wdathing/one-rom/hardware/3d/README.md

# One ROM 3D Models

This directory contains 3D printable models that may be useful for One ROM users.

All files in this directory tree are licensed under the [CERN Open Hardware Licence Version 2 - Weakly Reciprocal (CERN-OHL-W-2.0)](/LICENSE.md#cern-ohl-w-20-license).  See the [LICENSE](/LICENSE.md#cern-ohl-w-20-license) and [NOTICE](/hardware/NOTICE) files in the root of the repository for more details.
