wdathing/one-rom/hardware/pcb/verified/fire-24-g/README.md

# Fire 24 Rev G

An upright USB-C variant of fire-24-f - the connector sticks up out of the board rather than lying flat, which helps where there is too little room at the edge of One ROM to plug in a cable.  It is not preferred over fire-24-f - the two connector orientations are complementary.
