wdathing/one-rom/hardware/pcb/verified/fire-28-d/README.md

# Fire 28 Rev D

An upright USB-C variant of fire-28-c - the connector sticks up out of the board rather than lying flat, which helps where there is too little room at the edge of One ROM to plug in a cable.  It is not preferred over fire-28-c - the two connector orientations are complementary.

**Has components on both sides of the board.**
