wdathing/one-rom/hardware/pcb/verified/fire-32-c/README.md

# Fire 32 Rev C

An upright USB-C variant of fire-32-b2 - the connector sticks up out of the board rather than lying flat, which helps where there is too little room at the edge of One ROM to plug in a cable.  It is not preferred over fire-32-b2 - the two connector orientations are complementary.

**Has components on both sides of the board.**
