wdathing/one-rom/firmware/src/main.c

// One ROM Main startup code (clock and GPIO initialisation)

// Copyright (C) 2026 Piers Finlayson <piers@piers.rocks>
//
// MIT License

#include "include.h"
#ifdef UART_BOOT_TEST
#include "reg-rp235x.h"
#endif

int firmware_main(void) {
    // Platform specific initialization
    platform_specific_init();

    // Next step is to validate the minimum metadata required to continue.
    // Beyond here, code can assume onerom_info.metadata_header is present
    // and valid, as are ->hardware_info and ->firmware_config.
    if (!metadata_valid()) {
        // Enter bootloader
        ERR("Invalid metadata");
        enter_bootloader();
    }

    // Update any runtime info based on the metadata.
    update_runtime_from_metadata();

    // Next initialize the GPIOs very early on, to turn off the status LED and
    // read the ROM slot select pins.  Pins are part of the metadata, which is
    // why we had to check that first.
    setup_initial_gpios();

    // Enable logging.  Done after GPIO setup, so SWD pins are configured.
    if (BOOT_LOGGING_EN && !TURBO) {
        LOG_INIT();
    }

    // Do initial plugin parsing.  The system plugin can potentially override
    // USB DFU support, which is why we do it now.
    // Must be done even when turbo booting.
    DEBUG("Initial plugin parse");
    uint8_t disable_vbus_det, plugins, num_plugins;
    plugins = initial_plugin_parse(&disable_vbus_det, &num_plugins);

    // Set up VBUS detect interrupt if there's no plugin replacing USB
    // support.
    if (!disable_vbus_det) {
        DEBUG("Init VBUS det");
        setup_vbus_interrupt();
    } else {
        LOG("Plugin disabled VBUS detect");
    }

    // Log ROM slot information
    if (BOOT_LOGGING_EN && !TURBO) {
        log_roms();
    }

    // If turbo booting, skip the image select jumper reading
    uint32_t sel_mask = 0;
    uint32_t sel_pins = 0;
    if (!TURBO) {
        // Read image select pin values, as this allows us to figure out what
        // ROM slot to serve, which in turn might have some firmware configuration
        // overrides, like overclocking.
        sel_pins = check_sel_pins(&sel_mask);
    }

    // Get the chosen ROM slot based on the image select pins.
    if (METADATA->rom_slot_count > num_plugins) {
        // Figure out what ROM slot to use
        RUNTIME->rom_slot_index = get_rom_slot_index(sel_pins, sel_mask, plugins);

        // Get pointer to the selected ROM slot
        RUNTIME->current_rom_slot = &ROM_SLOTS[RUNTIME->rom_slot_index];

        // Now process any firmware overrides from the selected ROM slot.
        process_firmware_overrides(RUNTIME->current_rom_slot);
    } else {
        ERR("No ROM slots to serve");
    }

    // Initialize clock
    DEBUG("Init clock");
    setup_clock();

#ifdef UART_BOOT_TEST
    // Bring-up test only: continuously transmit 0x55 on UART1 (GPIO40 TX /
    // GPIO41 RX) from here - after clock setup, so RUNTIME->sysclk_mhz is
    // valid, but before ROM serving (PIOs/DMA) or any plugin ever starts.
    // Isolates UART1 bring-up completely from both.  Never returns.
    {
        CLOCK_PERI_CTRL = CLOCK_PERI_CTRL_ENABLE;

        RESET_RESET_SET = RESET_UART1;
        RESET_RESET_CLR = RESET_UART1;
        while (!(RESET_DONE & RESET_UART1)) { }

        GPIO_CTRL(40u) = GPIO_CTRL_FUNC_UART;
        GPIO_CTRL(41u) = GPIO_CTRL_FUNC_UART;
        // PAD_INPUT set on TX too, not just RX - confirmed against the SDK's
        // own gpio_set_function(), which enables the pad input buffer
        // unconditionally on every pin, output-only or not.
        GPIO_PAD(40u) = (GPIO_PAD(40u) | PAD_INPUT) & ~(uint32_t)(PAD_PU | PAD_PD | PAD_OUTPUT_DISABLE | PAD_ISO);
        GPIO_PAD(41u) = (GPIO_PAD(41u) | PAD_INPUT) & ~(uint32_t)(PAD_PU | PAD_PD | PAD_OUTPUT_DISABLE | PAD_ISO);

        uint32_t clk_peri_hz = (uint32_t)RUNTIME->sysclk_mhz * 1000000u;
        uint32_t baud = 115200u;
        uint64_t scaled = ((uint64_t)clk_peri_hz * 4u + (baud / 2u)) / baud;
        uint32_t ibrd = (uint32_t)(scaled >> 6);
        uint32_t fbrd = (uint32_t)(scaled & 0x3Fu);
        if (ibrd == 0u) {
            ibrd = 1u;
            fbrd = 0u;
        }

        UART_REG(UART1_BASE, UART_CR_OFFSET) = 0;
        UART_REG(UART1_BASE, UART_IBRD_OFFSET) = ibrd;
        UART_REG(UART1_BASE, UART_FBRD_OFFSET) = fbrd;
        UART_REG(UART1_BASE, UART_LCR_H_OFFSET) = UART_LCR_H_WLEN_8 | UART_LCR_H_FEN;
        UART_REG(UART1_BASE, UART_CR_OFFSET) = UART_CR_UARTEN | UART_CR_TXE | UART_CR_RXE;

        for (;;) {
            while (UART_REG(UART1_BASE, UART_FR_OFFSET) & UART_FR_TXFF) { }
            UART_REG(UART1_BASE, UART_DR_OFFSET) = 0x55u;
        }
    }
#endif // UART_BOOT_TEST

    // Set up the RAM table to serve the ROM from
    if (RUNTIME->current_rom_slot != NULL) {
        // We always preload to RAM slot 0
        RUNTIME->current_ram_slot = 0;

        preload_rom_image();
    }

    // Set up the status LED hardware now (unconditionally - the pin is
    // configured as an output whether or not the LED is currently on), so we
    // don't need to call the function from the main loop, which might be
    // running from RAM.
    DEBUG("Init LED");
    setup_status_led();

    // If no ROM slot is selected, enter limp mode now that the status LED is
    // setup.
    if (RUNTIME->current_rom_slot == NULL) {
        limp_mode(LIMP_MODE_NO_ROMS);
    }

    // Put the status LED where the configuration says, now we're ready to
    // serve the ROM.
    pio_led_boot();

    // Start serving the ROM.  This returns once the PIOs and DMAs have been
    // setup.  We return back to the reset handler in vector.c, which then
    // starts any plugins.  We do it from higher up the stack, so the minimum
    // stack is used for any plugin running on this core. 
    LOG("Setup ROM serving");

    // Shut SWD down before serving starts, if configured to do so.  Done last
    // so a probe is available for all of boot - including boot logging, which
    // rides RTT over SWD.  Nothing is logged beyond this point, and plugins
    // (started from vector.c once pio() returns) get no logging either.
    //
    // Cheap enough - a RAM test and a few register writes - to do even when
    // turbo booting.
    if (!RUNTIME->swd_enabled) {
        LOG("Disabling SWD");
        disable_swd();
    }

    return pio();
}
