wdathing/one-rom/docs/pdf/render.py

#!/usr/bin/env python3
"""Render the One ROM documentation set to PDF.

The set, and every string that appears in a PDF but not in its source markdown,
is defined in docs.toml.  Nothing document-specific is written here.

Cover text comes from the document itself: the title is the markdown's leading
H1 and the subtitle is the paragraph that follows it.  Every One ROM document
already opens by naming itself and saying in a sentence what it covers, so a
second copy of that text kept alongside the build would only be a copy to let
drift.  The H1 is dropped from the body, since the cover now carries it.

A document assembled from several markdown files is the exception: no one member
names the whole, so its cover text is declared in docs.toml, and every member
keeps its own H1 as a top-level heading.  This renders one file either way -
the assembling is done before this runs, by
`cargo run -p doc-gen --bin doc-assemble`, which writes <slug>.md into the same
output directory.  ci/build-docs.sh runs the two in order.  Neither calls the
other.

A manifest of what was built is written to the output directory, for
ci/build-docs.sh to stage from.
"""

import argparse
import datetime
import json
import re
import subprocess
import sys
import tomllib
from pathlib import Path

PDF_DIR = Path(__file__).resolve().parent

# A title may name the version of the thing it documents - COMPATIBILITY.md
# opens "One ROM Chip Compatibility - firmware v0.7.2".  The cover prints the
# version in its own right, so trim the clause rather than saying it twice.
TITLE_VERSION_CLAUSE = re.compile(r"\s*[-–—]\s*\S*\s*v\d+\.\d+\.\d+\s*$")

# Contents entries long enough to wrap read badly, and in CHIP-TYPES.md every
# pinout heading is "23QL384 - A composite ROM type, serving a combined ...".
# The body keeps the full heading, where the description earns its place - the
# contents keeps the part that identifies it.
TOC_TRUNCATE_OVER = 40
TOC_SPLIT = re.compile(r"\s+[-–—]\s+")

# A document written for GitHub may carry its own hand-written contents list,
# as CHIP-TYPES.md does.  The generated contents supersedes it, so it is
# dropped rather than printed twice.
HAND_WRITTEN_TOC = re.compile(r"^#{1,3}\s+(table of )?contents\s*$", re.I)

# How deep the contents goes for a document that does not say.  An assembled
# document spends its first level on member titles, so it usually says.
DEFAULT_TOC_DEPTH = 3

# A document may state a value that something else owns - a hold limit from the
# metadata schema, the CLI's own version - inside a marker naming that source:
#
#     the limit is <!--[const:GPIO_MAX_HOLD_MS:seconds]-->60 seconds<!--[/]-->.
#
# rust/doc-gen checks those values against their sources; this only has to take
# the markers back out before rendering, so a PDF carries the text and not the
# bookkeeping.  The delimiters are stated in both places, which is two copies of
# a punctuation choice rather than of a fact - change one and the other's tests
# say so.
MARKER = re.compile(r"<!--\[[^\]]*\]-->|<!--\[/\]-->")
MARKER_OPEN = re.compile(r"<!--\[(?!/)([^\]]*)\]-->")
MARKER_CLOSE = "<!--[/]-->"

NOT_PROSE = re.compile(
    r"""^(
        \#             |   # heading
        >              |   # block quote
        \|             |   # table row
        (```|~~~)      |   # fenced code
        ([-*+]\s)      |   # bullet list - the space matters, since a paragraph
                           # may open with an inline code span or emphasis
        (\d+\.\s)      |   # numbered list
        ([-*_]{3,}$)       # horizontal rule
    )""",
    re.X,
)


def git(root, *args):
    """Run git in the repository and return its trimmed stdout."""
    return subprocess.run(
        ["git", *args], capture_output=True, text=True, check=True, cwd=root,
    ).stdout.strip()


# -------------------------------------------------------------- versions --

def cli_version(root):
    """The onerom-cli crate version."""
    text = (root / "rust/cli/Cargo.toml").read_text()
    match = re.search(r'^version\s*=\s*"([^"]+)"', text, re.M)
    if not match:
        sys.exit("error: no version in rust/cli/Cargo.toml")
    return match.group(1)


def firmware_version(root):
    """The firmware version, from the root Makefile."""
    text = (root / "Makefile").read_text()
    parts = []
    for field in ("MAJOR", "MINOR", "PATCH"):
        match = re.search(rf"^VERSION_{field}\s*:?=\s*(\S+)", text, re.M)
        if not match:
            sys.exit(f"error: no VERSION_{field} in Makefile")
        parts.append(match.group(1))
    return ".".join(parts)


VERSION_READERS = {"cli": cli_version, "firmware": firmware_version}


# -------------------------------------------------------------- markdown --

def check_markers(text, origin):
    """Refuse a document whose markers would print into the PDF."""
    opens = len(MARKER_OPEN.findall(text))
    closes = text.count(MARKER_CLOSE)
    if opens != closes:
        sys.exit(
            f"error: {origin} has {opens} opening and {closes} closing value "
            f"markers.\n  An unclosed marker would print into the PDF.  Run "
            f"'cargo run -p doc-gen' to see where."
        )


def strip_markers(text):
    """The document as a reader sees it, with the value markers removed."""
    return MARKER.sub("", text)


def check_values(root, source, origin):
    """Check the values a document states against the sources that own them.

    Only for a document read from the working tree.  A past edition is read
    from a git ref, where its values are what they were then and the checker
    may not exist at all.

    ci/rust-tests.sh runs the same check, but a release is built by hand and
    the gate may not have been - and this is the last moment before a stale
    number is published as a PDF.
    """
    try:
        result = subprocess.run(
            ["cargo", "run", "-q", "-p", "doc-gen", "--bin", "doc-gen",
             "--", "--check", source],
            cwd=root / "rust",
            capture_output=True,
            text=True,
        )
    except FileNotFoundError:
        sys.exit(
            "error: cargo not found, so the values in "
            f"{origin} cannot be checked against their sources.\n  A document "
            "read from the working tree is checked before it is published.  "
            "Past\n  editions, which name a git ref, are not - build those "
            "without a Rust toolchain."
        )
    if result.returncode != 0:
        sys.exit(
            f"error: {origin} states values that no longer match their "
            f"sources:\n{result.stdout}{result.stderr}"
        )


def is_prose(line):
    """True if a stripped line opens an ordinary paragraph."""
    return not NOT_PROSE.match(line)


def strip_inline_markup(text):
    """Reduce inline markdown to the plain text behind it."""
    text = re.sub(r"\[([^\]]*)\]\([^)]*\)", r"\1", text)  # links
    text = re.sub(r"[`*_]", "", text)
    return text.strip()


def drop_hand_written_toc(lines):
    """Remove a hand-written contents section, up to the next heading."""
    out = []
    skipping = False
    for line in lines:
        if HAND_WRITTEN_TOC.match(line):
            skipping = True
            continue
        if skipping:
            if line.startswith("#"):
                skipping = False
            else:
                continue
        out.append(line)
    return out


def read_document(text, origin):
    """Return (title, subtitle, body) for a markdown document."""
    lines = text.split("\n")

    title = None
    start = 0
    for i, line in enumerate(lines):
        if line.startswith("# "):
            title = TITLE_VERSION_CLAUSE.sub("", strip_inline_markup(line[2:]))
            start = i + 1
            break
    if title is None:
        sys.exit(f"error: {origin} has no leading H1 to use as a title")

    subtitle = ""
    paragraph = []
    for line in lines[start:]:
        stripped = line.strip()
        if not stripped:
            if paragraph:
                break
            continue
        if not is_prose(stripped):
            if paragraph:
                break
            continue
        paragraph.append(stripped)
    if paragraph:
        subtitle = strip_inline_markup(" ".join(paragraph))

    body = drop_hand_written_toc(lines[:start - 1] + lines[start:])
    return title, subtitle, "\n".join(body)


def shorten_toc(html):
    """Trim over-long contents entries to their identifying part."""

    def trim(match):
        opening, text = match.group(1), match.group(2)
        if len(text) > TOC_TRUNCATE_OVER:
            head = TOC_SPLIT.split(text, maxsplit=1)[0]
            if head != text and len(head) >= 3:
                text = head
        return f"{opening}{text}</a>"

    start = html.find('<nav id="TOC"')
    end = html.find("</nav>", start)
    if start < 0 or end < 0:
        return html
    toc = re.sub(r"(<a\b[^>]*>)([^<]*)</a>", trim, html[start:end])
    return html[:start] + toc + html[end:]


# ----------------------------------------------------------------- build --

def members_of(document, slug):
    """The document's members, or None where it names a single source."""
    members = document.get("members")
    if members and "source" in document:
        sys.exit(
            f"error: {slug}: has both source and members.\n  A document is one "
            f"file or a list of them, not both - drop whichever is not what you "
            f"meant."
        )
    if not members and "source" not in document:
        sys.exit(f"error: {slug}: has neither source nor members")
    return members


def render(document, config, root, out_dir, commit, date, year):
    project = config["project"]
    slug = document["slug"]

    version_source = document["version_source"]
    if version_source not in config["version_sources"]:
        sys.exit(f"error: {slug}: unknown version source '{version_source}'")
    spec = config["version_sources"][version_source]

    # A source may state its version outright rather than being read from the
    # tree.  That is what lets a past edition be rebuilt: the working tree says
    # what the CLI is now, not what it was at the ref being rendered.
    if "version" in spec:
        version = spec["version"]
    else:
        version = VERSION_READERS[version_source](root)
    label = spec["label"].format(version=version)

    members = members_of(document, slug)
    ref = document.get("ref")

    # A document may name a git ref, and is then read from the object store
    # rather than the working tree - no checkout, and this tree is untouched.
    # The cover is stamped with that ref's commit, so it does not misattribute
    # the text to whatever HEAD happens to be.
    if members:
        if ref:
            sys.exit(
                f"error: {slug}: names both members and a ref.\n  An assembled "
                f"document is built from the working tree.  A past edition names "
                f"one\n  file, as it shipped."
            )
        sources = [member["source"] for member in members]
        assembled = out_dir / f"{slug}.md"
        if not assembled.exists():
            sys.exit(
                f"error: {slug} is assembled from {', '.join(sources)}, and "
                f"{assembled} is not there.\n  Run 'cargo run -p doc-gen --bin "
                f"doc-assemble -- --out-dir {out_dir}' first, or run\n  "
                f"ci/build-docs.sh, which runs the two in order."
            )
        text = assembled.read_text()
        origin = ", ".join(sources)
        for source in sources:
            check_values(root, source, source)
    elif ref:
        text = git(root, "show", f"{ref}:{document['source']}")
        commit = git(root, "rev-parse", "--short", f"{ref}^{{commit}}")
        origin = f"{ref}:{document['source']}"
    else:
        text = (root / document["source"]).read_text()
        origin = document["source"]
        check_values(root, origin, origin)

    check_markers(text, origin)
    text = strip_markers(text)

    # A document may also state its version in its own prose, for readers of the
    # markdown on GitHub, who get no cover and no versioned filename.  That is a
    # second statement of the same fact, so it is checked rather than trusted -
    # a manual must not be published whose banner disagrees with its cover.
    banner = document.get("version_banner")
    if banner:
        expected = banner.format(version=version)
        if expected not in text:
            sys.exit(
                f"error: {origin} does not say \"{expected}\".\n"
                f"  The version being published is {version}. Update the "
                f"document's own version statement to match, or correct the "
                f"version source."
            )

    if members:
        # Declared rather than read: the cover names the whole document, and no
        # member of it does.  Each member's H1 stays in the body as a top-level
        # heading, so nothing is dropped here.
        for key in ("title", "subtitle"):
            if key not in document:
                sys.exit(
                    f"error: {slug}: is assembled from members, so it needs a "
                    f"{key} - no member names the whole document."
                )
        title = strip_inline_markup(document["title"])
        subtitle = strip_inline_markup(document["subtitle"])
        body = text
    else:
        title, subtitle, body = read_document(text, origin)
        # A single-source document takes its cover from the markdown, which is
        # what a reader on GitHub sees first.  Where the document set says
        # otherwise it wins - a cover has a line to fill and a page to fill it
        # on, and the markdown's opening sentence is written for neither.
        if "title" in document:
            title = strip_inline_markup(document["title"])
        if "subtitle" in document:
            subtitle = strip_inline_markup(document["subtitle"])

    html = subprocess.run(
        [
            "pandoc",
            "--from=gfm",
            "--to=html5",
            "--standalone",
            f"--template={PDF_DIR / 'template.html'}",
            "--toc",
            f"--toc-depth={document.get('toc_depth', DEFAULT_TOC_DEPTH)}",
            "--metadata", f"title={title}",
            "--metadata", f"subtitle={subtitle}",
            "--metadata", f"versionlabel={label}",
            "--metadata", f"date={date}",
            "--metadata", f"commit={commit}",
            "--metadata", f"repo={project['repo']}",
            "--metadata", f"source={origin}",
            # The contents page groups its entries by member, which only makes
            # sense where the top level is member titles.
            *(["--metadata", "assembled=true"] if members else []),
            "--metadata", f"wordmark={project['name']}",
            "--metadata", f"url={project['url']}",
            "--metadata", f"notice={project['cover_notice'].format(year=year)}",
        ],
        input=body,
        capture_output=True,
        text=True,
        check=True,
    ).stdout

    stem = f"{project['file_prefix']}{slug}"
    html_path = out_dir / f"{stem}.html"
    html_path.write_text(shorten_toc(html))

    footer = project["footer_notice"].format(year=year).replace("'", "\\27 ")

    built = []
    for paper, paper_spec in config["papers"].items():
        # The page size, the cover height that depends on it, and the footer
        # notice are the only style values that cannot be static.
        paper_css = out_dir / f"paper-{paper}.css"
        paper_css.write_text(
            f"@page {{ size: {paper_spec['size']} }}\n"
            f"@page cover {{ size: {paper_spec['size']} }}\n"
            f"@page toc {{ size: {paper_spec['size']} }}\n"
            f".cover {{ height: {paper_spec['height']} }}\n"
            f"@page {{ @bottom-left {{ content: '{footer}' }} }}\n"
        )
        pdf = out_dir / f"{stem}-{version}-{paper}.pdf"
        subprocess.run(
            [
                "weasyprint",
                "--base-url", f"{PDF_DIR}/",
                "--stylesheet", str(PDF_DIR / "docs.css"),
                "--stylesheet", str(paper_css),
                str(html_path),
                str(pdf),
            ],
            check=True,
        )
        paper_css.unlink()
        built.append({"paper": paper, "filename": pdf.name})

    html_path.unlink()
    built_document = {
        "slug": slug,
        "source": origin,
        "tracks_label": spec.get("short_label", version_source),
        "title": title,
        # The document's opening sentence doubles as its catalogue description,
        # the way a plugin's releases.json carries one.
        "description": subtitle,
        "version": version,
        "tracks": version_source,
        "files": built,
    }

    # Every document this PDF was made from, in order, so a catalogue reader can
    # reach the always-current markdown.  A list in every case - a PDF made from
    # one document has a list of one - because a PDF made from several has no
    # single source and there is nothing for a reader to prefer.  These are
    # repository-relative paths, not `origin`, which names a git ref for a past
    # edition.
    built_document["sources"] = sources if members else [document["source"]]

    return built_document


def main():
    parser = argparse.ArgumentParser()
    parser.add_argument("--config", default=str(PDF_DIR / "docs.toml"))
    parser.add_argument("--out-dir", required=True)
    parser.add_argument(
        "--source",
        help="build only documents on this version source, e.g. cli or firmware",
    )
    args = parser.parse_args()

    root = PDF_DIR.parent.parent
    config = tomllib.loads(Path(args.config).read_text())

    out_dir = Path(args.out_dir)
    out_dir.mkdir(parents=True, exist_ok=True)

    commit = git(root, "rev-parse", "--short", "HEAD")
    today = datetime.date.today()
    date = f"{today.day} {today:%B %Y}"

    # A version source is the release cycle a document follows, so selecting one
    # selects the documents that ship with it.  The CLI manual moves with the
    # onerom-cli crate and the chip references with the firmware, and the two
    # release separately - building the whole set from either would republish
    # documents whose version had not moved.
    documents_to_build = config["documents"]
    if args.source:
        if args.source not in config["version_sources"]:
            sys.exit(f"error: unknown version source '{args.source}'")
        documents_to_build = [
            d for d in documents_to_build if d["version_source"] == args.source
        ]
        if not documents_to_build:
            sys.exit(f"error: no documents on version source '{args.source}'")

    documents = []
    for document in documents_to_build:
        print(f"building {document['slug']}")
        documents.append(
            render(document, config, root, out_dir, commit, date, today.year)
        )

    manifest = {"version": 1, "commit": commit, "date": today.isoformat(),
                "documents": documents}
    (out_dir / "build-manifest.json").write_text(json.dumps(manifest, indent=2))


if __name__ == "__main__":
    main()
